plb500/AutoBloomer-HIB/pico/pico_src/sensor_definitions.c

#include "sensor_definitions.h" 

I2CMultiplexer sensorI2CMultiplexer = {
    .mMultiplexerAddress        = DEFAULT_MULTIPLEXER_ADDRESS,
    .mResetPin                  = SENSOR_I2C_MULTIPLEXER_RESET_PIN,
};

// I2C bus controller
I2CInterface sensorI2CInterface = {
    .mI2C = SENSOR_I2C,
    .mBaud = SENSOR_I2C_BAUDRATE,
    .mSDA = SENSOR_I2C_SDA_PIN,
    .mSCL = SENSOR_I2C_SCL_PIN,
    .mMultiplexer = &sensorI2CMultiplexer
};

SonarPIOWrapper PIO_WRAPPER = {
    .mPIO = pio0,
    .mInitialized = false
};

Sensor sensorsList[NUM_SENSORS] = {
    {
        .mSensorDefinition = {                               
            .mSensor = {
                .mSonarSensor = {
                    .mTXPin = SONAR_SENSOR_L1_TX_PIN,
                    .mRXPin = SONAR_SENSOR_L1_RX_PIN,
                    .mBaudrate = SONAR_SENSOR_BAUDRATE,
                    .mStateMachineID = 0,
                    .mPIOWrapper = &PIO_WRAPPER
                }
            },
            .mSensorType = SONAR_SENSOR,
            .mSensorID = SONAR_SENSOR_L1_ID,
            .mSensorConnectLEDPosition = SONAR_SENSOR_L1_ACTIVE_LED,
            .mHardwareConnectionID = FEED_SENSOR_L1_CONNECT_ID
        }
    },
    {
        .mSensorDefinition = {                               
            .mSensor = {
                .mSonarSensor = {
                    .mTXPin = SONAR_SENSOR_R1_TX_PIN,
                    .mRXPin = SONAR_SENSOR_R1_RX_PIN,
                    .mBaudrate = SONAR_SENSOR_BAUDRATE,
                    .mStateMachineID = 1,
                    .mPIOWrapper = &PIO_WRAPPER
                }
            },
            .mSensorType = SONAR_SENSOR,
            .mSensorID = SONAR_SENSOR_R1_ID,
            .mSensorConnectLEDPosition = SONAR_SENSOR_R1_ACTIVE_LED,
            .mHardwareConnectionID = FEED_SENSOR_R1_CONNECT_ID
        }
    },
    {
        .mSensorDefinition = {                               
            .mSensor = {
                .mSensorPod = {
                    .mInterface = &sensorI2CInterface,
                    .mI2CChannel = I2C_CHANNEL_0,
                    .mSCD30Address = SCD30_I2C_ADDRESS,
                    .mSoilSensorAddress = SOIL_SENSOR_3_ADDRESS,
                }
            },
            .mSensorType = SENSOR_POD,
            .mSensorID = SENSOR_POD_L_ID,
            .mSensorConnectLEDPosition = SENSOR_POD_L_ACTIVE_LED,
            .mHardwareConnectionID = I2C_DEVICE_0_CONNECT_ID
        }
    },
    {
        .mSensorDefinition = {                               
            .mSensor = {
                .mSensorPod = {
                    .mInterface = &sensorI2CInterface,
                    .mI2CChannel = I2C_CHANNEL_7,
                    .mSCD30Address = SCD30_I2C_ADDRESS,
                    .mSoilSensorAddress = SOIL_SENSOR_1_ADDRESS,
                }
            },
            .mSensorType = SENSOR_POD,
            .mSensorID = SENSOR_POD_R_ID,
            .mSensorConnectLEDPosition = SENSOR_POD_R_ACTIVE_LED,
            .mHardwareConnectionID = I2C_DEVICE_7_CONNECT_ID
        }
    },
    {
        .mSensorDefinition = {                               
            .mSensor = {
                .mBatterySensor = {
                    .mEnableSensePin = BATTERY_SENSE_ENABLE_PIN,
                    .mBatteryMeasurePin = BATTERY_SENSE_PIN,
                    .mADCInput = RTC_BATTERY_ADC_PORT
                }
            },
            .mSensorType = BATTERY_SENSOR,
            .mSensorID = RTC_BATTERY_SENSOR,
            .mSensorConnectLEDPosition = NO_LED,
            .mHardwareConnectionID = ALWAYS_CONNECTED_CONNECT_ID
        }
    }
};


                        ///////////////////////////////////////////////////////
                        // Sensor output descriptions for connected hardware //
                        ///////////////////////////////////////////////////////

// Static reading definitions
MsgPackSensorReadingDescription MPACK_SONAR_READING_DESCRIPTION = {
    0,                                      // mReadingID
    "Distance (mm)",                        // mReadingName
    INT_READING,                            // mType   
    {.mIntValue=30},                        // mMinValue
    {.mIntValue=4500}                       // mMaxValue
};

MsgPackSensorReadingDescription MPACK_CO2_READING_DESCRIPTION = {
    0,                                      // mReadingID
    "Carbon Dioxide (PPM)",                 // mReadingName
    FLOAT_READING,                          // mType   
    {.mFloatValue=400.0f},                  // mMinValue
    {.mFloatValue=4000.0f}                  // mMaxValue
};

MsgPackSensorReadingDescription MPACK_TEMPERATURE_READING_DESCRIPTION = {
    1,                                      // mReadingID
    "Temperature (°C)",                     // mReadingName
    FLOAT_READING,                          // mType   
    {.mFloatValue=10.0f},                   // mMinValue
    {.mFloatValue=65.0f}                    // mMaxValue
};

MsgPackSensorReadingDescription MPACK_HUMIDITY_READING_DESCRIPTION = {
    2,                                      // mReadingID
    "RH (%)",                               // mReadingName
    FLOAT_READING,                          // mType   
    {.mFloatValue=0.0f},                    // mMinValue
    {.mFloatValue=100.0f}                   // mMaxValue
};

MsgPackSensorReadingDescription MPACK_SOIL_MOISTURE_READING_DESCRIPTION = {
    3,
    "Soil Moisture",                        // mReadingName
    INT_READING,                            // mType   
    {.mIntValue=0},                         // mMinValue
    {.mIntValue=2000}                       // mMaxValue
};

MsgPackSensorReadingDescription MPACK_BATTERY_READING_DESCRIPTION = {
    0,                                      // mReadingID
    "Voltage",                              // mReadingName
    FLOAT_READING,                          // mType   
    {.mFloatValue=0.f},                     // mMinValue
    {.mFloatValue=3.3f}                     // mMaxValue
};


                        /////////////////////////////////////////////////
                        // Sensor data wrappers for connected hardware //
                        /////////////////////////////////////////////////

MsgPackSensorPacket sensorPackets[NUM_SENSORS] = {
    {
        .mSensorID = SONAR_SENSOR_L1_ID,
        .mSensorName = "Feed Level Sensor L1",
        .mSensorType = SONAR_SENSOR,
        .mCalibrationParams = {
            .mIsCalibratable = false,
            .mCalibrationValueType = FLOAT_READING,
            .mCalibrationRangeMin = {.mFloatValue=0.f},
            .mCalibrationRangeMax = {.mFloatValue=50.f}
        },
        .mCurrentSensorData = {
            .mStatus = SENSOR_DISCONNECTED,
            .mNumReadings = 1,
            .mSensorReadings = (MsgPackSensorReading[1]) {
                {
                    .mDescription = &MPACK_SONAR_READING_DESCRIPTION,
                    .mValue = {
                        .mIntValue=0
                    }
                }    
            }
        }
    },
    {
        .mSensorID = SONAR_SENSOR_R1_ID,
        .mSensorName = "Feed Level Sensor R1",
        .mSensorType = SONAR_SENSOR,
        .mCalibrationParams = {
            .mIsCalibratable = false,
            .mCalibrationValueType = FLOAT_READING,
            .mCalibrationRangeMin = {.mFloatValue=0.f},
            .mCalibrationRangeMax = {.mFloatValue=50.f}
        },
        .mCurrentSensorData = {
            .mStatus = SENSOR_DISCONNECTED,
            .mNumReadings = 1,
            .mSensorReadings = (MsgPackSensorReading[1]) {
                {
                    .mDescription = &MPACK_SONAR_READING_DESCRIPTION,
                    .mValue = {
                        .mIntValue=0
                    }
                }    
            }
        }
    },
    {
        .mSensorID = SENSOR_POD_L_ID,
        .mSensorName = "Sensor Pod L",
        .mSensorType = SENSOR_POD,
        .mCalibrationParams = {
            .mIsCalibratable = false,
            .mCalibrationValueType = FLOAT_READING,
            .mCalibrationRangeMin = {.mFloatValue=0.f},
            .mCalibrationRangeMax = {.mFloatValue=50.f}
        },
        .mCurrentSensorData = {
            .mStatus = SENSOR_DISCONNECTED,
            .mNumReadings = 4,
            .mSensorReadings = (MsgPackSensorReading[4]) {
                {
                    .mDescription = &MPACK_CO2_READING_DESCRIPTION,
                    .mValue = {
                        .mFloatValue = 0.f
                    }
                },
                {
                    .mDescription = &MPACK_TEMPERATURE_READING_DESCRIPTION,
                    .mValue = {
                        .mFloatValue=0.f
                    }
                },
                {
                    .mDescription = &MPACK_HUMIDITY_READING_DESCRIPTION,
                    .mValue = {
                        .mFloatValue=0.f
                    }
                },
                {
                    .mDescription = &MPACK_SOIL_MOISTURE_READING_DESCRIPTION,
                    .mValue = {
                        .mIntValue=0
                    }
                },
            }
        }
    },
    {
        .mSensorID = SENSOR_POD_R_ID,
        .mSensorName = "Sensor Pod R",
        .mSensorType = SENSOR_POD,
        .mCalibrationParams = {
            .mIsCalibratable = false,
            .mCalibrationValueType = FLOAT_READING,
            .mCalibrationRangeMin = {.mFloatValue=0.f},
            .mCalibrationRangeMax = {.mFloatValue=50.f}
        },
        .mCurrentSensorData = {
            .mStatus = SENSOR_DISCONNECTED,
            .mNumReadings = 4,
            .mSensorReadings = (MsgPackSensorReading[4]) {
                {
                    .mDescription = &MPACK_CO2_READING_DESCRIPTION,
                    .mValue = {
                        .mFloatValue = 0.f
                    }
                },
                {
                    .mDescription = &MPACK_TEMPERATURE_READING_DESCRIPTION,
                    .mValue = {
                        .mFloatValue=0.f
                    }
                },
                {
                    .mDescription = &MPACK_HUMIDITY_READING_DESCRIPTION,
                    .mValue = {
                        .mFloatValue=0.f
                    }
                },
                {
                    .mDescription = &MPACK_SOIL_MOISTURE_READING_DESCRIPTION,
                    .mValue = {
                        .mIntValue=0
                    }
                },
            }
        }
    },
    {
        .mSensorID = RTC_BATTERY_SENSOR,
        .mSensorName = "RTC Battery",
        .mSensorType = BATTERY_SENSOR,
        .mCalibrationParams = {
            .mIsCalibratable = false,
            .mCalibrationValueType = FLOAT_READING,
            .mCalibrationRangeMin = {.mFloatValue=0.f},
            .mCalibrationRangeMax = {.mFloatValue=50.f}
        },
        .mCurrentSensorData = {
            .mStatus = SENSOR_DISCONNECTED,
            .mNumReadings = 1,
            .mSensorReadings = (MsgPackSensorReading[1]) {
                {
                    .mDescription = &MPACK_BATTERY_READING_DESCRIPTION,
                    .mValue = {
                        .mFloatValue=0.f
                    }
                }    
            }
        }
    }
};
