plb500/AutoBloomer-HIB/sensor_simulator/sensor_simulator.ino

#include "cmd_buffer.h"
#include "sensor_msgpack_data.h"
#include "fake_sensors.h"

const size_t MPACK_OUT_BUFFER_SIZE = 512;
const unsigned long HEARTBEAT_TIMEOUT = 5000;

CommandBuffer cmdBuffer;
char mpackBuffer[MPACK_OUT_BUFFER_SIZE];

unsigned long statusLEDOffTime = 0;
unsigned long nextHeartbeatTime = 0;


void send_heartbeat() {
    PackResponse response;

    // Pack and send the header data
    response = pack_heartbeat_packet(mpackBuffer, MPACK_OUT_BUFFER_SIZE);
    if(!response.mErrorCode) {
        Serial.write(mpackBuffer, response.mBytesUsed);
    }

    // Pack and send terminator packet
    response = pack_terminator_packet(HEARTBEAT_PACKET, mpackBuffer, MPACK_OUT_BUFFER_SIZE);
    if(!response.mErrorCode) {
        Serial.write(mpackBuffer, response.mBytesUsed);
    }

    nextHeartbeatTime = (millis() + HEARTBEAT_TIMEOUT);
}
    
void send_controller_ready() {
    PackResponse response;

    // Pack and send the header data
    response = pack_controller_ready_packet(mpackBuffer, MPACK_OUT_BUFFER_SIZE);
    if(!response.mErrorCode) {
        Serial.write(mpackBuffer, response.mBytesUsed);
    }

    // Pack and send terminator packet
    response = pack_terminator_packet(CONTROLLER_READY_PACKET, mpackBuffer, MPACK_OUT_BUFFER_SIZE);
    if(!response.mErrorCode) {
        Serial.write(mpackBuffer, response.mBytesUsed);
    }
}

void handle_send_all_sensor_data_command() {
    PackResponse response;
    HeaderPacket headerPacket = {
        GET_ALL_SENSOR_VALUES,
        COMMAND_OK,
    };

    // Pack and send the header data
    response = pack_header_data(headerPacket, mpackBuffer, MPACK_OUT_BUFFER_SIZE);
    if(!response.mErrorCode) {
        Serial.write(mpackBuffer, response.mBytesUsed);
    }

    // Pack and send sensor data
    for(int i = 0; i < NUM_FAKE_SENSORS; ++i) {
        response = pack_sensor_data(FAKE_SENSORS[i], mpackBuffer, MPACK_OUT_BUFFER_SIZE);
        if(!response.mErrorCode) {
            Serial.write(mpackBuffer, response.mBytesUsed);
        }
    }

    // Pack and send terminator packet
    response = pack_terminator_packet(GET_ALL_SENSOR_VALUES, mpackBuffer, MPACK_OUT_BUFFER_SIZE);
    if(!response.mErrorCode) {
        Serial.write(mpackBuffer, response.mBytesUsed);
    }
}

void handle_send_sensor_data_command(uint8_t sensorID) {
    PackResponse response;
    HeaderPacket headerPacket = {
        GET_SENSOR_VALUE,
        COMMAND_OK    
    };

    // Check for bad sensor ID
    if(sensorID >= NUM_FAKE_SENSORS) {
        headerPacket.mResponseCode = SENSOR_NOT_FOUND;
    }
    
    
    // Pack and send the header data
    response = pack_header_data(headerPacket, mpackBuffer, MPACK_OUT_BUFFER_SIZE);
    if(!response.mErrorCode) {
        Serial.write(mpackBuffer, response.mBytesUsed);
    }

    // Pack and send sensor data
    if(sensorID < NUM_FAKE_SENSORS) {
        response = pack_sensor_data(FAKE_SENSORS[sensorID], mpackBuffer, MPACK_OUT_BUFFER_SIZE);
        if(!response.mErrorCode) {
            Serial.write(mpackBuffer, response.mBytesUsed);
        }
    }            

    // Pack and send terminator packet
    response = pack_terminator_packet(GET_SENSOR_VALUE, mpackBuffer, MPACK_OUT_BUFFER_SIZE);
    if(!response.mErrorCode) {
        Serial.write(mpackBuffer, response.mBytesUsed);
    }
}

void handle_command(SensorCommandIdentifier cmd, uint8_t *argumentBytes) {
    uint8_t sensorID = 0;

    switch(cmd) {
        case GET_ALL_SENSOR_VALUES:
            handle_send_all_sensor_data_command();
            break;
        case GET_SENSOR_VALUE:
            sensorID = argumentBytes[0];
            handle_send_sensor_data_command(sensorID);
            break;
        case NO_COMMAND:
        default:
            break;
    }
    
    init_cmd_buffer(&cmdBuffer);
}

void setup() {
    // Setup incoming command buffer
    init_cmd_buffer(&cmdBuffer);

    // Status LED
    pinMode(LED_BUILTIN, OUTPUT);

    // Setup serial
    Serial.begin(115200);

    // Send ready signal
    send_controller_ready();
}

void loop() {
    uint8_t *argumentBytes;
    unsigned long currentTime = millis();
    
    while(Serial.available()) {
        statusLEDOffTime = (currentTime + 250);
        handle_incoming_byte(&cmdBuffer, Serial.read());
    }

    if(currentTime > statusLEDOffTime) {
        digitalWrite(LED_BUILTIN, LOW);
    } else {
        digitalWrite(LED_BUILTIN, HIGH);
    }

    if(currentTime > nextHeartbeatTime) {
        send_heartbeat();
    }

    switch(cmdBuffer.mCommandBufferState) {
        case AWAITING_DATA:
        case PROCESSING_COMMAND_DATA:
            break;
        case HAS_COMPLETE_COMMAND:
            argumentBytes = &(cmdBuffer.mCommandBuffer[1]);
            handle_command(cmdBuffer.mCurrentCommand, argumentBytes);
            init_cmd_buffer(&cmdBuffer);            
            break;
        case HAS_INVALID_COMMAND_DATA:
            init_cmd_buffer(&cmdBuffer);
            break;
        default:
            break;
    }
}
